jirihusak/majordomus/HW/RoomSens/FW/RoomSens.X/drivers/motion_EKMC.h

/* 
 * File:   motion_EKMC.h
 * Author: jiri
 *
 * Created on December 30, 2017, 8:40 PM
 */

#ifndef MOTION_EKMC_H
#define	MOTION_EKMC_H

void motion_Init();
void motion_Task();
uint8_t motion_get_detector();

#endif	/* MOTION_EKMC_H */
