jirihusak/majordomus/HW/RoomSens/FW/RoomSens.X/drivers/adc_internal.c

/**
  ADCC Generated Driver File

  @Company
    Microchip Technology Inc.

  @File Name
    adcc.c

  @Summary
    This is the generated driver implementation file for the ADCC driver using PIC10 / PIC12 / PIC16 / PIC18 MCUs

  @Description
    This source file provides implementations for driver APIs for ADCC.
    Generation Information :
        Product Revision  :  PIC10 / PIC12 / PIC16 / PIC18 MCUs - 1.81.6
        Device            :  PIC18F57K42
        Driver Version    :  2.1.4
    The generated drivers are tested against the following:
        Compiler          :  XC8 2.30 and above
        MPLAB             :  MPLAB X 5.40
*/

/*
    (c) 2018 Microchip Technology Inc. and its subsidiaries. 
    
    Subject to your compliance with these terms, you may use Microchip software and any 
    derivatives exclusively with Microchip products. It is your responsibility to comply with third party 
    license terms applicable to your use of third party software (including open source software) that 
    may accompany Microchip software.
    
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
    IN NO EVENT WILL MICROCHIP BE LIABLE FOR ANY INDIRECT, SPECIAL, PUNITIVE, 
    INCIDENTAL OR CONSEQUENTIAL LOSS, DAMAGE, COST OR EXPENSE OF ANY KIND 
    WHATSOEVER RELATED TO THE SOFTWARE, HOWEVER CAUSED, EVEN IF MICROCHIP 
    HAS BEEN ADVISED OF THE POSSIBILITY OR THE DAMAGES ARE FORESEEABLE. TO 
    THE FULLEST EXTENT ALLOWED BY LAW, MICROCHIP'S TOTAL LIABILITY ON ALL 
    CLAIMS IN ANY WAY RELATED TO THIS SOFTWARE WILL NOT EXCEED THE AMOUNT 
    OF FEES, IF ANY, THAT YOU HAVE PAID DIRECTLY TO MICROCHIP FOR THIS 
    SOFTWARE.
*/

/**
  Section: Included Files
*/

#include <xc.h>
#include "adc_internal.h"

/**
  Section: ADCC Module Variables
*/

/**
  Section: ADCC Module APIs
*/

void ADC_Internal_Initialize(void)
{
    // set the ADCC to the options selected in the User Interface
    // ADLTH 0; 
    ADLTHL = 0x00;
    // ADLTH 0; 
    ADLTHH = 0x00;
    // ADUTH 0; 
    ADUTHL = 0x00;
    // ADUTH 0; 
    ADUTHH = 0x00;
    // ADSTPT 0; 
    ADSTPTL = 0x00;
    // ADSTPT 0; 
    ADSTPTH = 0x00;
    // ADACC 0; 
    ADACCU = 0x00;
    // ADRPT 0; 
    ADRPT = 0x00;
    // ADPCH ANA0; 
    ADPCH = 0x00;
    // ADACQ 128; 
    ADACQL = 0x80;
    // ADACQ 0; 
    ADACQH = 0x00;
    // ADCAP Additional uC disabled; 
    ADCAP = 0x00;
    // ADPRE 0; 
    ADPREL = 0x00;
    // ADPRE 0; 
    ADPREH = 0x00;
    // ADDSEN enabled; ADGPOL digital_low; ADIPEN disabled; ADPPOL Vss; 
    ADCON1 = 0x01;
    // ADCRS 0; ADMD Average_mode; ADACLR disabled; ADPSIS RES; 
    ADCON2 = 0x02;
    // ADCALC First derivative of Single measurement; ADTMD disabled; ADSOI ADGO not cleared; 
    ADCON3 = 0x00;
    // ADMATH registers not updated; 
    ADSTAT = 0x00;
    // ADNREF VSS; ADPREF VDD; 
    ADREF = 0x00;
    // ADACT disabled; 
    ADACT = 0x00;
    // ADCS FOSC/128; 
    ADCLK = 0x3F;
    // ADGO stop; ADFM right; ADON enabled; ADCS FOSC/ADCLK; ADCONT disabled; 
    ADCON0 = 0x84;
    

}

void ADC_Internal_StartConversion(adcc_channel_t channel)
{
    // select the A/D channel
    ADPCH = channel;      
  
    // Turn on the ADC module
    ADCON0bits.ADON = 1;

    // Start the conversion
    ADCON0bits.ADGO = 1;
}

bool ADC_Internal_IsConversionDone(void)
{
    // Start the conversion
    return ((unsigned char)(!ADCON0bits.ADGO));
}

adc_result_t ADC_Internal_GetConversionResult(void)
{
    // Return the result
    return ((adc_result_t)((ADRESH << 8) + ADRESL));
}

adc_result_t ADC_Internal_GetSingleConversion(adcc_channel_t channel)
{
    // select the A/D channel
    ADPCH = channel;  

    // Turn on the ADC module
    ADCON0bits.ADON = 1;
	
    //Disable the continuous mode.
    ADCON0bits.ADCONT = 0;    

    // Start the conversion
    ADCON0bits.ADGO = 1;


    // Wait for the conversion to finish
    while (ADCON0bits.ADGO)
    {
    }
    
    
    // Conversion finished, return the result
    return ((adc_result_t)((ADRESH << 8) + ADRESL));
}

void ADC_Internal_StopConversion(void)
{
    //Reset the ADGO bit.
    ADCON0bits.ADGO = 0;
}

void ADC_InternalC_SetStopOnInterrupt(void)
{
    //Set the ADSOI bit.
    ADCON3bits.ADSOI = 1;
}

void ADC_Internal_DischargeSampleCapacitor(void)
{
    //Set the ADC channel to AVss.
    ADPCH = 0x3b;   
}

void ADC_Internal_LoadAcquisitionRegister(uint16_t acquisitionValue)
{
    //Load the ADACQH and ADACQL registers.
    ADACQH = acquisitionValue >> 8; 
    ADACQL = acquisitionValue;  
}

void ADC_Internal_SetPrechargeTime(uint16_t prechargeTime)
{
    //Load the ADPREH and ADPREL registers.
    ADPREH = prechargeTime >> 8;  
    ADPREL = prechargeTime;
}

void ADC_Internal_SetRepeatCount(uint8_t repeatCount)
{
    //Load the ADRPT register.
    ADRPT = repeatCount;   
}

uint8_t ADC_Internal_GetCurrentCountofConversions(void)
{
    //Return the contents of ADCNT register
    return ADCNT;
}

void ADC_Internal_ClearAccumulator(void)
{
    //Reset the ADCON2bits.ADACLR bit.
    ADCON2bits.ADACLR = 1;
}

uint24_t ADC_Internal_GetAccumulatorValue(void)
{
    //Return the contents of ADACCU, ADACCH and ADACCL registers
    return (((uint24_t)ADACCU << 16)+((uint24_t)ADACCH << 8) + ADACCL);
}

bool ADC_Internal_HasAccumulatorOverflowed(void)
{
    //Return the status of ADSTATbits.ADAOV
    return ADSTATbits.ADAOV;
}

uint16_t ADC_Internal_GetFilterValue(void)
{
    //Return the contents of ADFLTRH and ADFLTRL registers
    return ((uint16_t)((ADFLTRH << 8) + ADFLTRL));
}

uint16_t ADC_Internal_GetPreviousResult(void)
{
    //Return the contents of ADPREVH and ADPREVL registers
    return ((uint16_t)((ADPREVH << 8) + ADPREVL));
}

void ADC_Internal_DefineSetPoint(uint16_t setPoint)
{
    //Sets the ADSTPTH and ADSTPTL registers
    ADSTPTH = setPoint >> 8;
    ADSTPTL = setPoint;
}

void ADC_Internal_SetUpperThreshold(uint16_t upperThreshold)
{
    //Sets the ADUTHH and ADUTHL registers
    ADUTHH = upperThreshold >> 8;
    ADUTHL = upperThreshold;
}

void ADC_Internal_SetLowerThreshold(uint16_t lowerThreshold)
{
    //Sets the ADLTHH and ADLTHL registers
    ADLTHH = lowerThreshold >> 8;
    ADLTHL = lowerThreshold;
}

uint16_t ADC_Internal_GetErrorCalculation(void)
{
	//Return the contents of ADERRH and ADERRL registers
	return ((uint16_t)((ADERRH << 8) + ADERRL));
}

void ADC_Internal_EnableDoubleSampling(void)
{
    //Sets the ADCON1bits.ADDSEN
    ADCON1bits.ADDSEN = 1;
}

void ADC_Internal_EnableContinuousConversion(void)
{
    //Sets the ADCON0bits.ADCONT
    ADCON0bits.ADCONT = 1;
}

void ADC_Internal_DisableContinuousConversion(void)
{
    //Resets the ADCON0bits.ADCONT
    ADCON0bits.ADCONT = 0;
}

bool ADC_Internal_HasErrorCrossedUpperThreshold(void)
{
    //Returns the value of ADSTATbits.ADUTHR bit.
    return ADSTATbits.ADUTHR;
}

bool ADC_Internal_HasErrorCrossedLowerThreshold(void)
{
    //Returns the value of ADSTATbits.ADLTHR bit.
    return ADSTATbits.ADLTHR;
}

uint8_t ADC_Internal_GetConversionStageStatus(void)
{
    //Returns the contents of ADSTATbits.ADSTAT field.
    return ADSTATbits.ADSTAT;
}

void ADC_Internal_Disable()
{
    ADCON0 = 0;
    ADCON1 = 0;
    ADCON2 = 0;
    ADCON3 = 0;
    ADACT = 0;
    // Clear the ADC Threshold interrupt flag
    PIR1bits.ADTIF = 0;
    // Enabling ADCC threshold interrupt.
    PIE1bits.ADTIE = 0;
}

uint16_t ADC_Internal_Get_Millivolts(adcc_channel_t channel)
{
    uint32_t result = 0;
    
    uint8_t i;
    for (i = 0; i < 16; i++) {
        result += ADC_Internal_GetSingleConversion(channel);
    }
    
    result = (result * 3300) >> 16; // divide 65536 (4096 * 16)
    
    return result;
}


/**
 End of File
*/
