jirihusak/majordomus/HW/RoomIO/FW/RoomIO.X/app.h

/* 
 * File:   app.h
 * Author: jiri
 *
 * Created on 14. prosince 2017, 22:20
 */

#ifndef APP_H
#define	APP_H

#include <stdint.h>
#include <stdbool.h>
#include <pic18.h>

#define BOARD_TYPE              "RoomIO"
#define APP_VERSION             "0.3"
#define BUILD_DATE              __DATE__ 


#define SYSTEM_CPU_HIGH_SPEED { CPUDOZEbits.DOZE = 0; CPUDOZEbits.DOZEN = 0; }
#define SYSTEM_CPU_LOW_POWER { CPUDOZEbits.DOZE = 5; CPUDOZEbits.DOZEN = 1;}

typedef struct {
    uint16_t power;
    uint16_t power_outputs;
    uint16_t adc0;
    uint16_t adc1;
   
    int16_t temperature_ext_0;  
    int16_t temperature_ext_1;  

} meas_struct_t;

extern meas_struct_t meas_values;

void app_Init();
void app_Task();




#endif	/* APP_H */
