jirihusak/majordomus/HW/RoomIO/FW/RoomIO.X/drivers/temp_TMP1075.h

/* 
 * File:   temp_TMP1075_H.h
 * Author: husak

 */

#ifndef TEMP_TMP1075_H
#define	TEMP_TMP1075_H

#ifdef	__cplusplus
extern "C" {
#endif
    
    void temp_TMP1075_init();
    int32_t temp_TMP1075_read_temperature();




#ifdef	__cplusplus
}
#endif

#endif	/* TEMP_TMP1075_H */
