jirihusak/majordomus/HW/RoomIO/FW/RoomIO.X/serial_interface.h

/* 
 * File:   serial_interface.h
 * Author: husak
 *
 * Created on 6. ?íjna 2019, 22:05
 */

#ifndef SERIAL_INTERFACE_H
#define	SERIAL_INTERFACE_H

void serialInterface_init();

void serialInterface_process();



#endif	/* SERIAL_INTERFACE_H */
